svenpetersen1965/Ultimate-64-Keyboard-Adapter/Rev. 0/pictures/IMG_5148.JPG

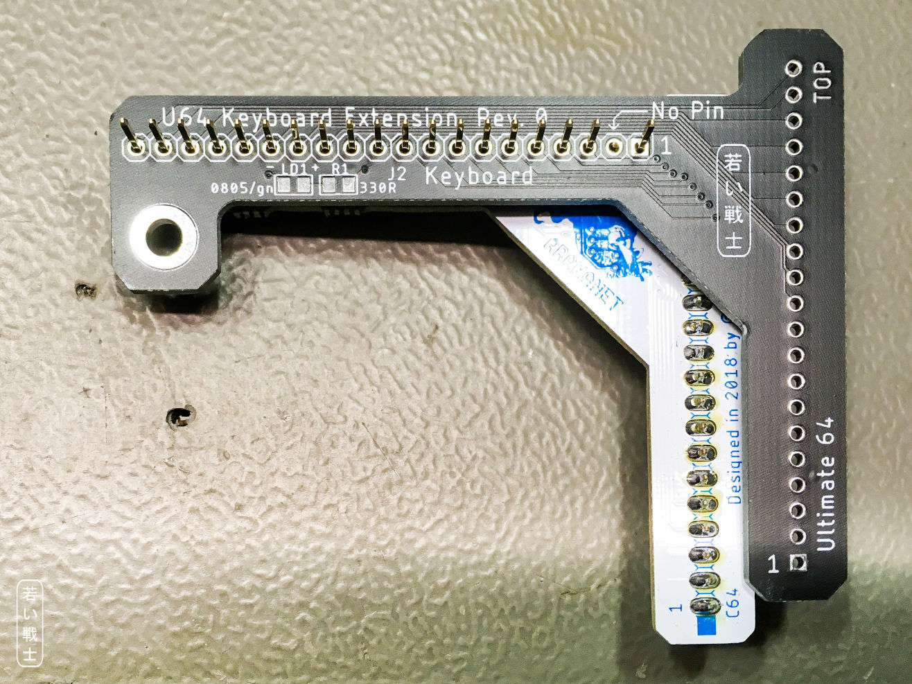
Rev. 0/pictures/IMG_5148.JPG
